andy5211d/Standig-899D/Pictures/IMG_0624.JPG

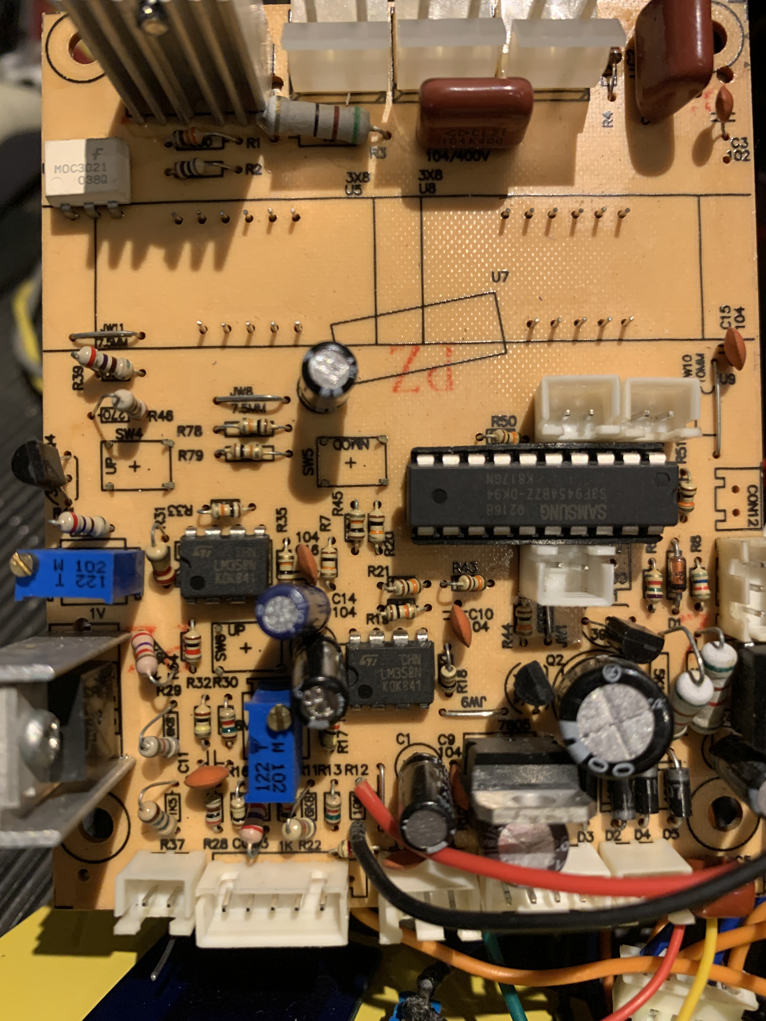
Pictures/IMG_0624.JPG
