andy5211d/Standig-899D/Pictures/IMG_0712.JPG

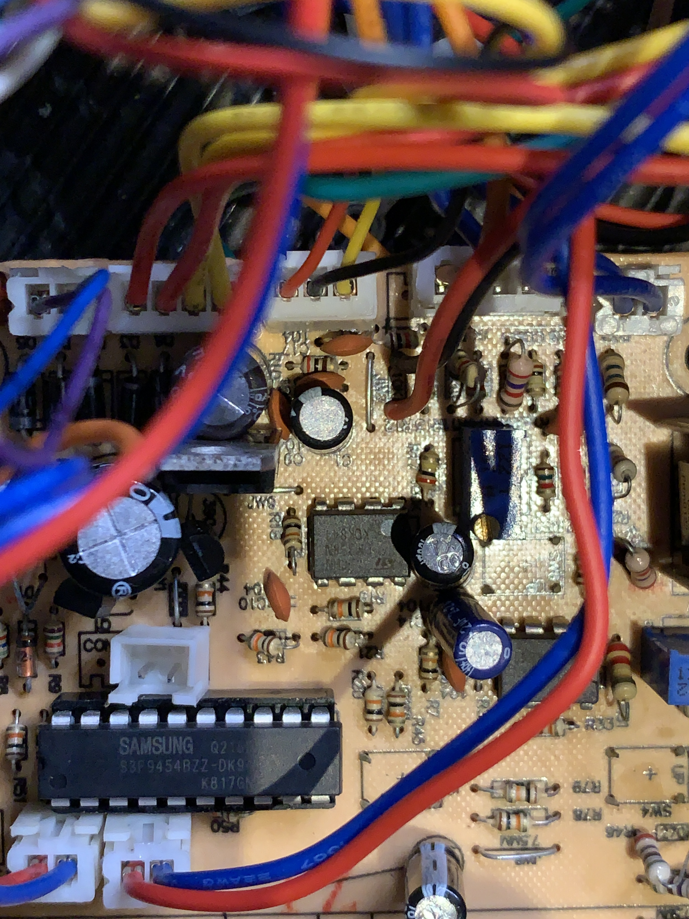
Pictures/IMG_0712.JPG
