andy5211d/Standig-899D/Pictures/IMG_0713.JPG

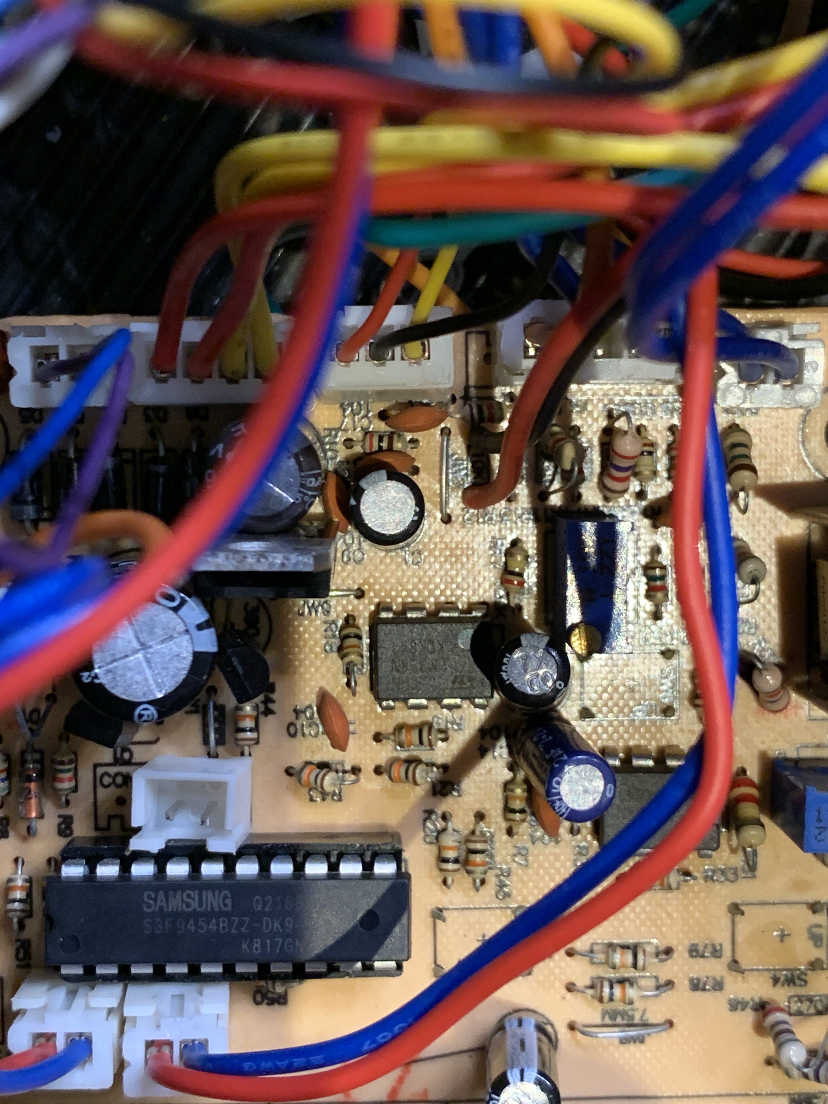
Pictures/IMG_0713.JPG
