andy5211d/Standig-899D/Pictures/IMG_0714.JPG

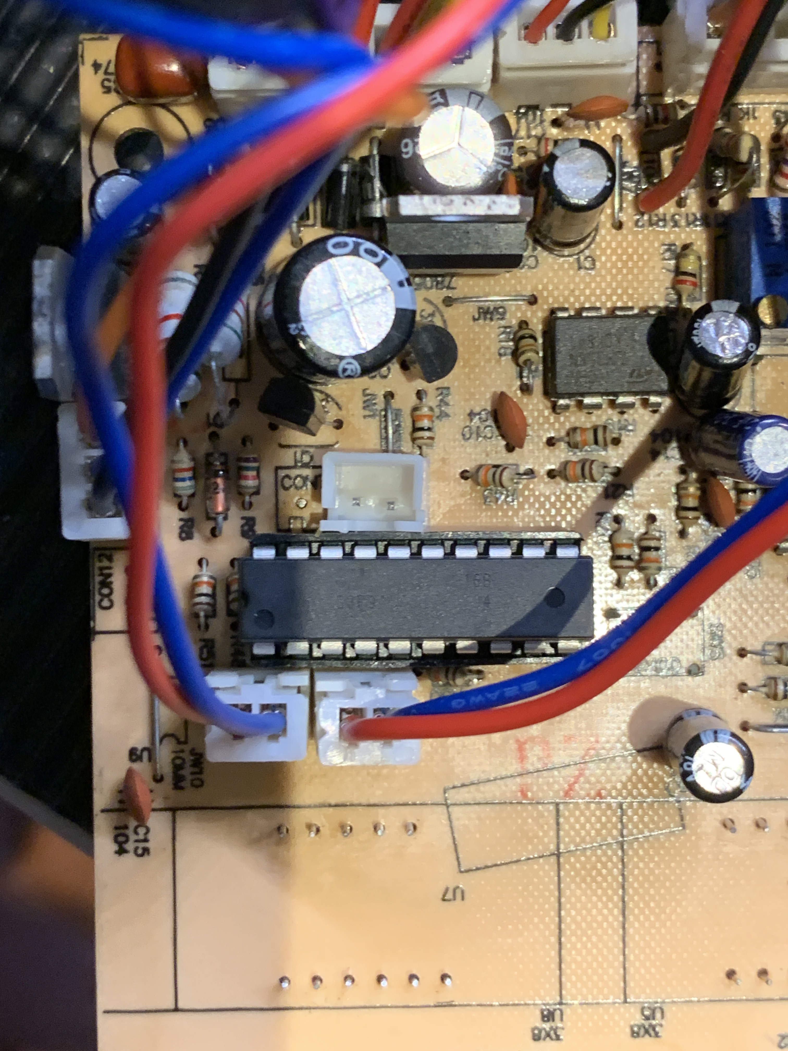
Pictures/IMG_0714.JPG
