andy5211d/Standig-899D/Pictures/IMG_0717.JPG

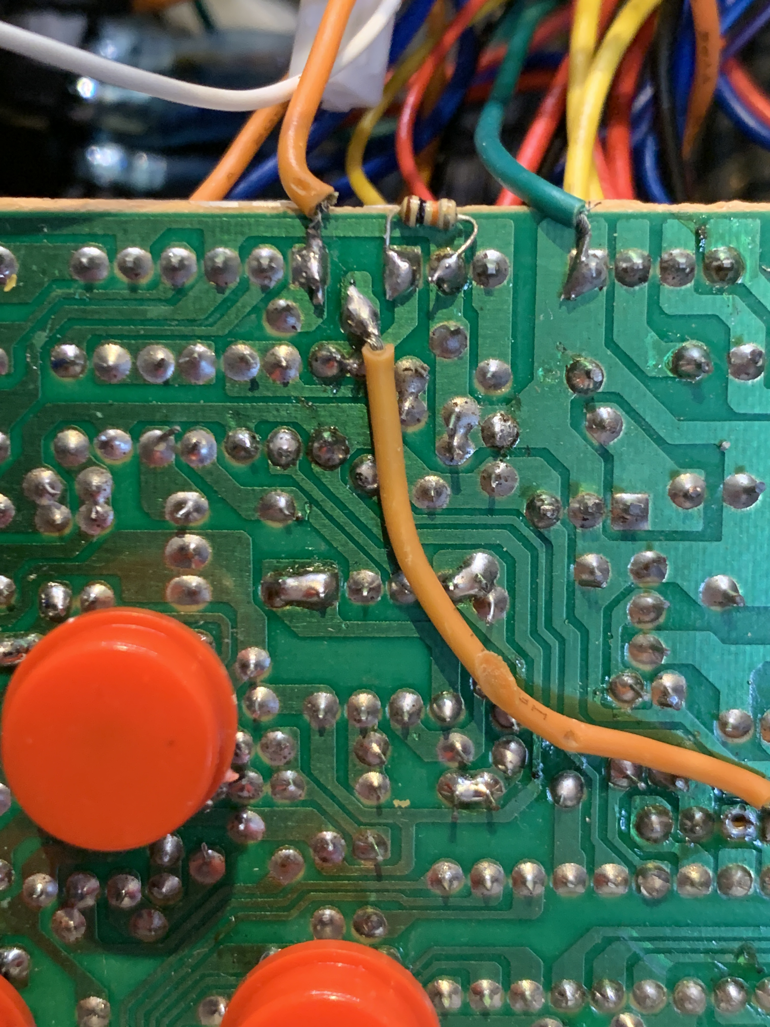
Pictures/IMG_0717.JPG
