andy5211d/Standig-899D/Pictures/IMG_0718.JPG

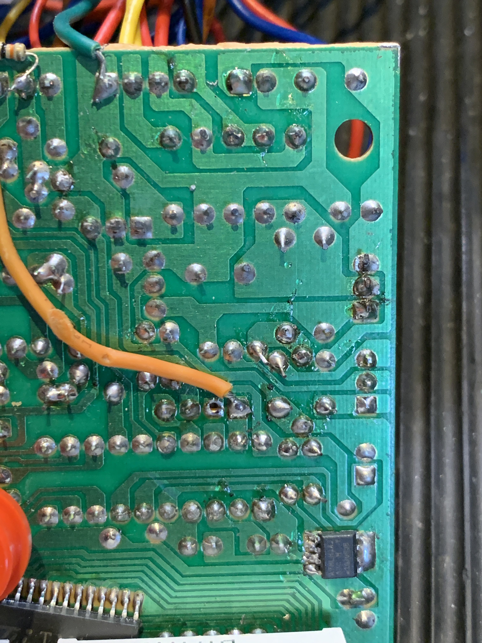
Pictures/IMG_0718.JPG
