andy5211d/Standig-899D/Pictures/IMG_0719.JPG

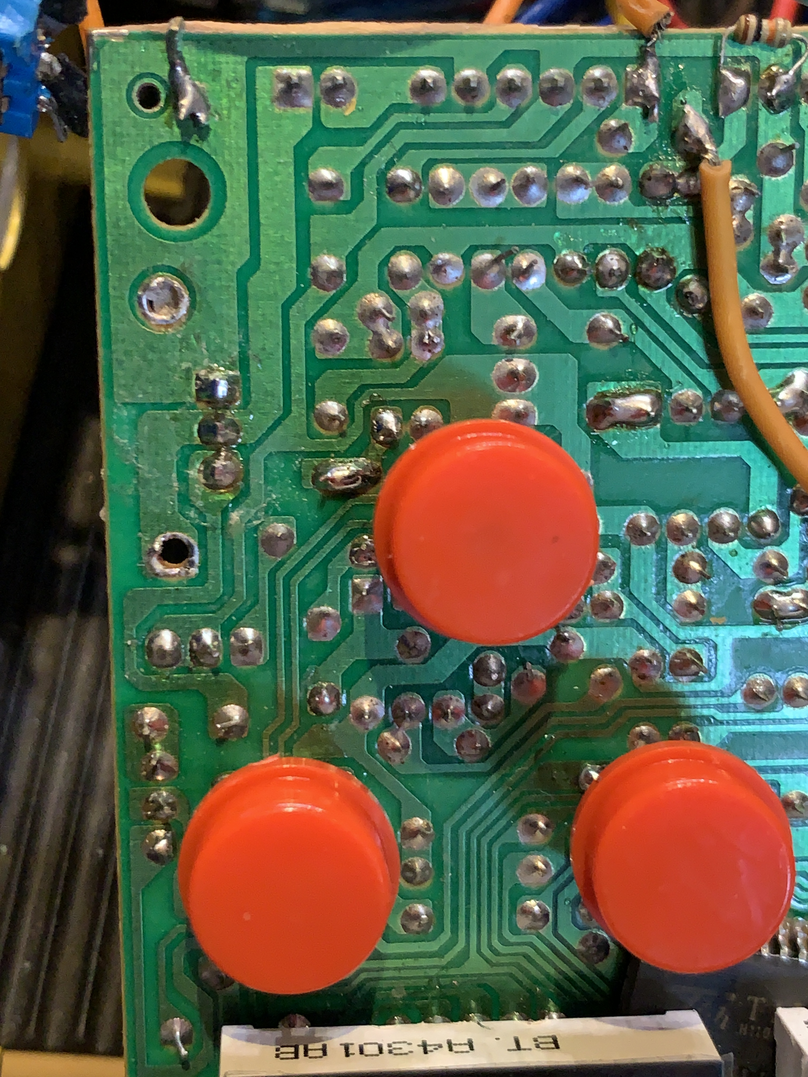
Pictures/IMG_0719.JPG
