andy5211d/Standig-899D/Pictures/IMG_0721.JPG

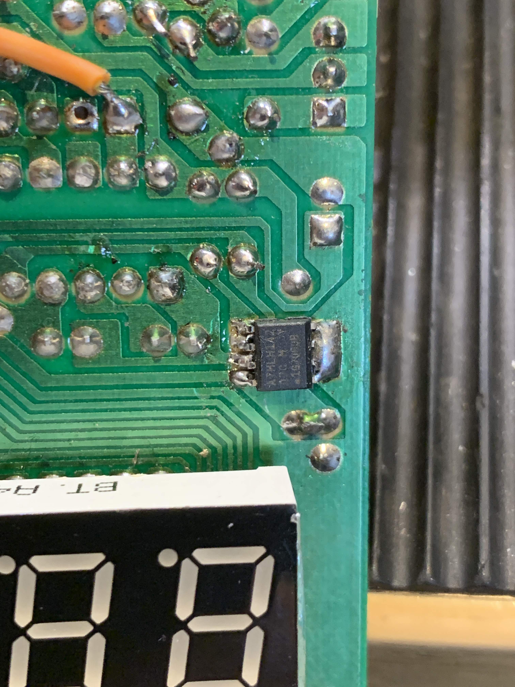
Pictures/IMG_0721.JPG
