andy5211d/Standig-899D/schematic/899d.kicad_sch

## KiCad design schematic/899d.kicad_sch (2024-03-28)

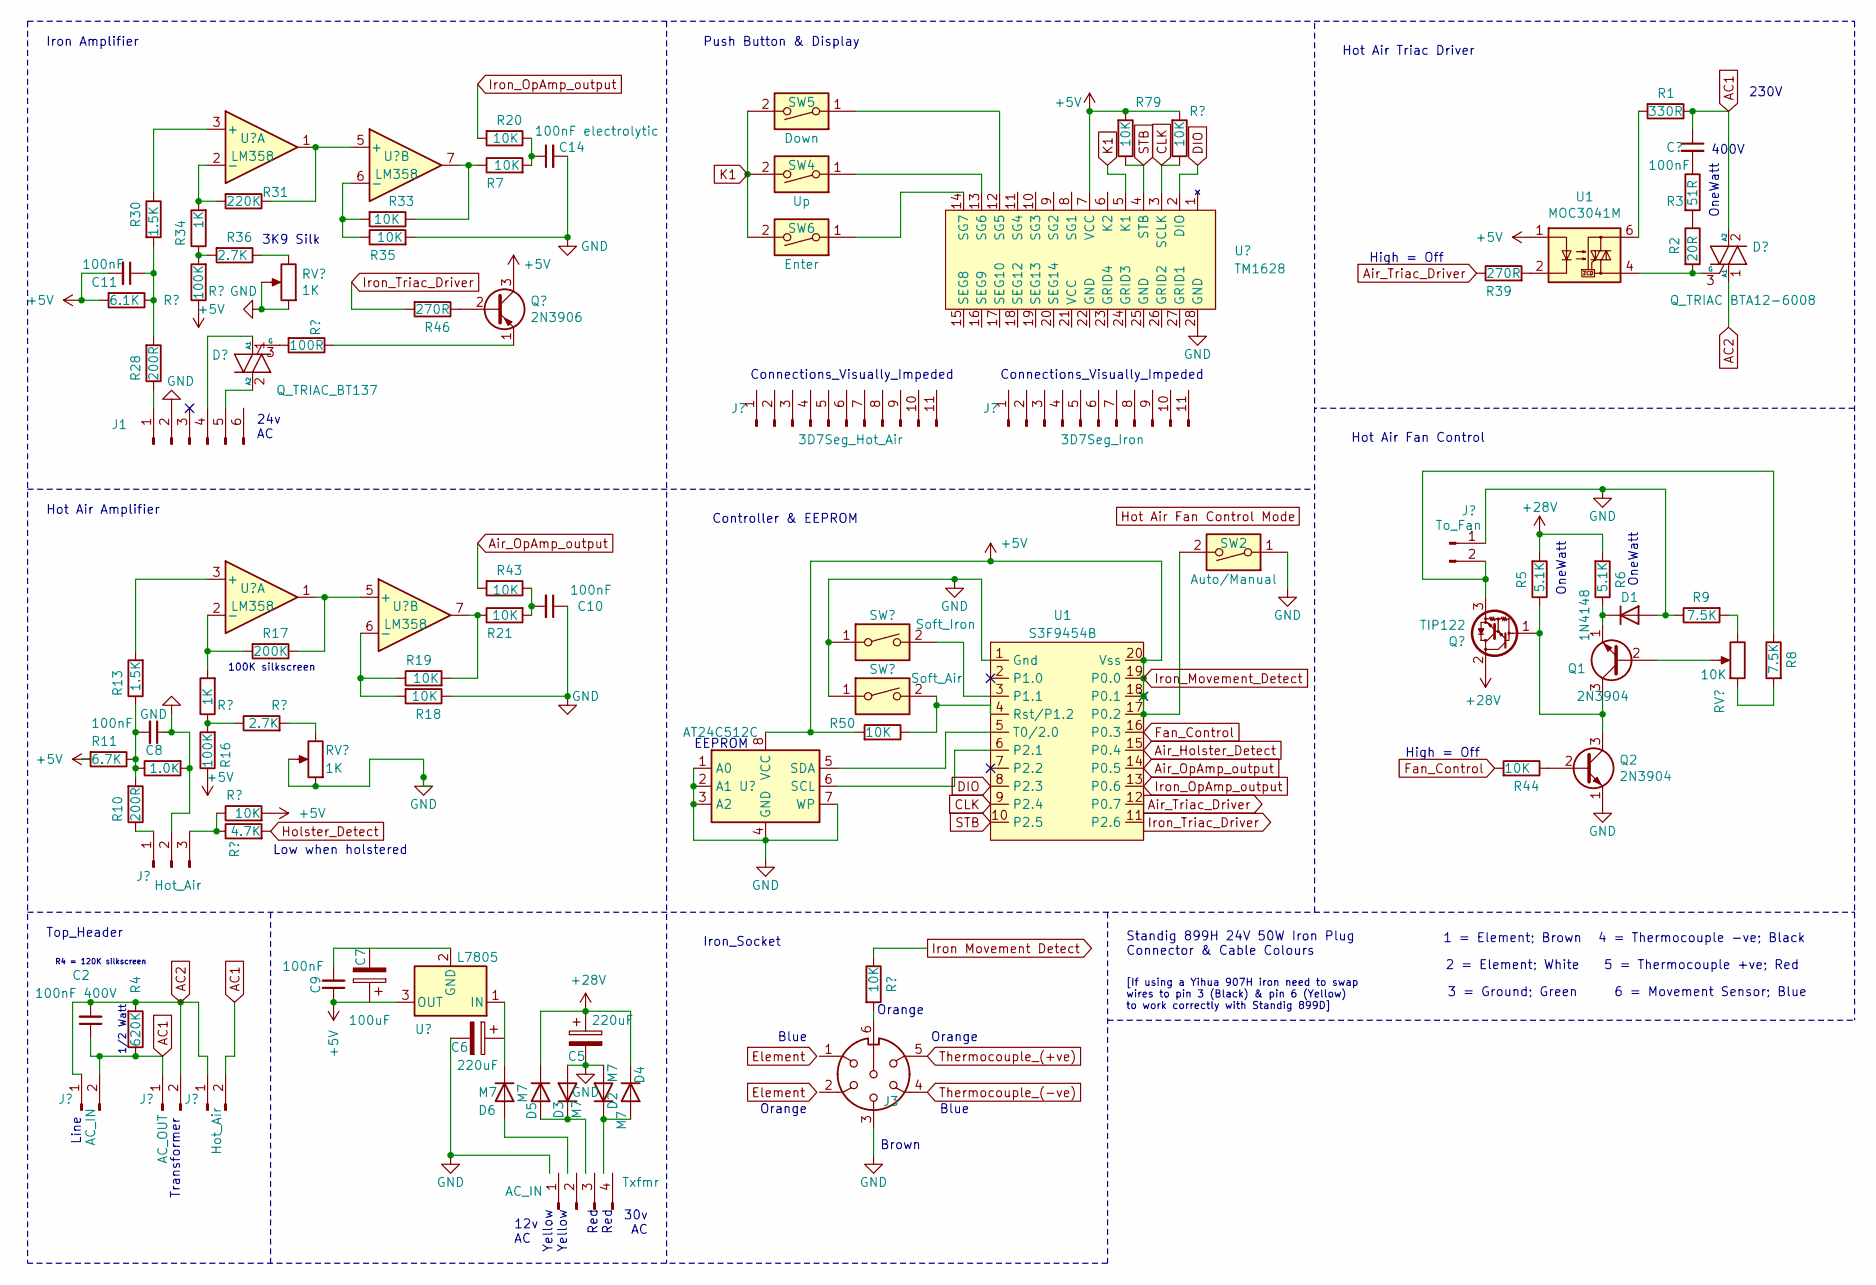
[picture p19: schematic 899d.kicad_sch]

Parts:
C2: 100nF 400V
C5, C6: 220uF
C7: 100uF
C8, C9, C10, C11: 100nF
C14: 100nF electrolytic
D1: 1N4148; D_DO-35_SOD27_P7.62mm_Horizontal
D2, D3, D4, D5, D6: M7; D_DO-41_SOD81_P10.16mm_Horizontal
J1, J3: (no value)
Q1, Q2: 2N3904; TO-92_Inline
R1: 330R
R2: 20R
R3: 51R
R4: 620K
R5, R6: 5.1K
R7, R18, R19, R20, R21, R33, R35, R43, R44, R50, R79: 10K
R8, R9: 7.5K
R10, R28: 200R
R11: 6.7K
R13, R30: 1.5K
R16: 100K
R17: 200K
R31: 220K
R34: 1K
R36: 2.7K
R39, R46: 270R
SW2: Auto/Manual
SW4: Up
SW5: Down
SW6: Enter
Txfmr: AC_IN
U1: MOC3041M

Connections:
AC1: C2.1, R1.1, R4.1
AC2: C2.2, R4.2
Air_Holster_Detect: U1.15 (P0.4)
Air_OpAmp_output: R43.2, U1.14 (P0.5)
Air_Triac_Driver: R39.1, U1.12 (P0.7)
CLK: U1.9 (P2.4)
DIO: U1.8 (P2.3)
Fan_Control: R44.2, U1.16 (P0.3)
GND: J3.3, SW2.1
Iron_Movement_Detect: R50.2, SW2.2, U1.17 (P0.2), U1.18 (P0.1), U1.19 (P0.0), U1.20 (Vss)
Iron_OpAmp_output: R20.2, U1.13 (P0.6)
Iron_Triac_Driver: R46.2, U1.11 (P2.6)
K1: SW4.2, SW5.2, SW6.2
unnamed: C5.1, D4.1 (K), D5.1 (K)
unnamed: C5.2, D2.2 (A), D3.2 (A)
unnamed: C8.1, R3.2
unnamed: C8.2, R3.1, R10.2, R11.1, R13.1
unnamed: C10.1, R18.1
unnamed: C10.2, R21.2, R43.1
unnamed: C11.1, R28.2, R30.2
unnamed: C14.1, R7.2, R20.1
unnamed: C14.2, R35.2
unnamed: D1.1 (K), Q1.1 (E), R6.1
unnamed: D1.2 (A), R9.1
unnamed: D2.1 (K), D4.2 (A)
unnamed: D3.1 (K), D5.2 (A)
unnamed: J1.1, R28.1
unnamed: Q1.3 (C), Q2.3 (C), R5.1
unnamed: Q2.2 (B), R44.1
unnamed: R1.2, U1.6 (P2.1)
unnamed: R2.1, R3.2
unnamed: R2.2, U1.4 (Rst/P1.2)
unnamed: R5.2, R6.2
unnamed: R18.2, R19.1
unnamed: R19.2, R21.1
unnamed: R31.2, R34.2
unnamed: R7.1, R33.1
unnamed: R33.2, R35.1
unnamed: R34.1, R36.2
unnamed: R39.2, U1.2 (P1.0)
unnamed: R50.1, U1.4 (Rst/P1.2)
STB: R79.1, U1.10 (P2.5)

Notes on the sheet:
12v AC
High = Off
Hot Air Triac Driver
Blue
400V
Yellow Yellow
4 = Thermocouple -ve; Black
Standig 899H 24V 50W Iron Plug Connector & Cable Colours
OneWatt
Hot Air Fan Control
EEPROM
3 = Ground; Green
100K silkscreen
1/2 Watt
1 = Element; Brown
[If using a Yihua 907H iron need to swap wires to pin 3 (Black) & pin 6 (Yellow) to work correctly with Standig 899D]
230V
Brown
5 = Thermocouple +ve; Red
Line
Low when holstered
Orange
24v AC
30v AC
Connections_Visually_Impeded
Push Button & Display
Transformer
3K9 Silk
Iron Amplifier
Iron_Socket
R4 = 120K silkscreen
2 = Element; White
6 = Movement Sensor; Blue
Hot Air Amplifier
Controller & EEPROM
Red Red
Top_Header
