andy5211d/Standig-899D/Pictures/IMG_0621.JPG

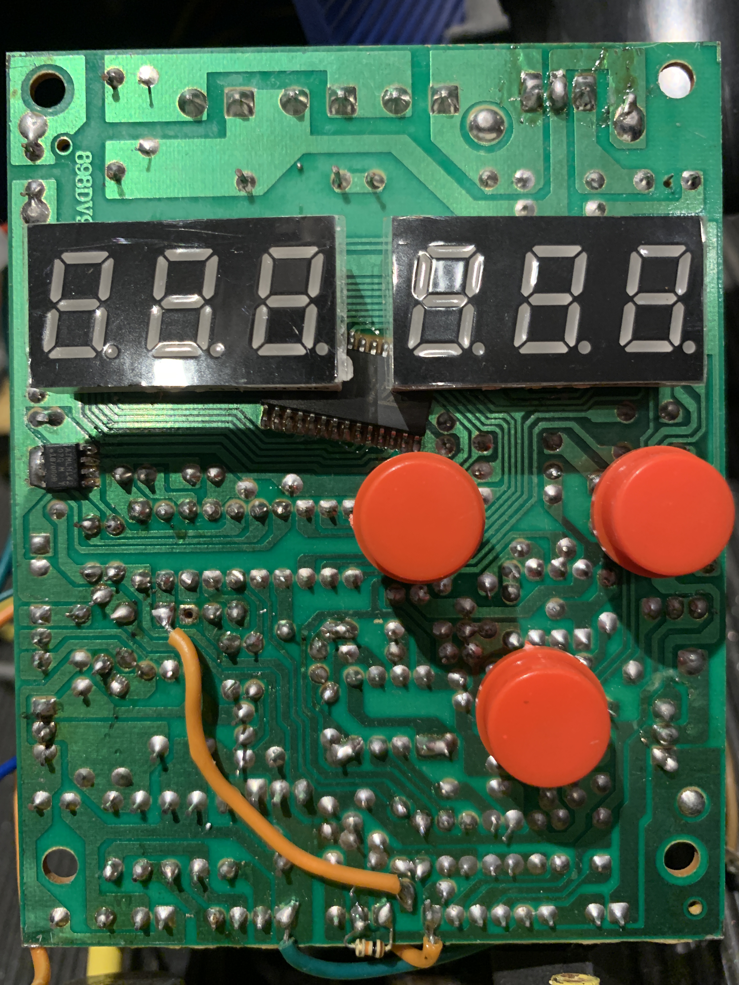
Pictures/IMG_0621.JPG
