andy5211d/Standig-899D/Pictures/IMG_0622.JPG

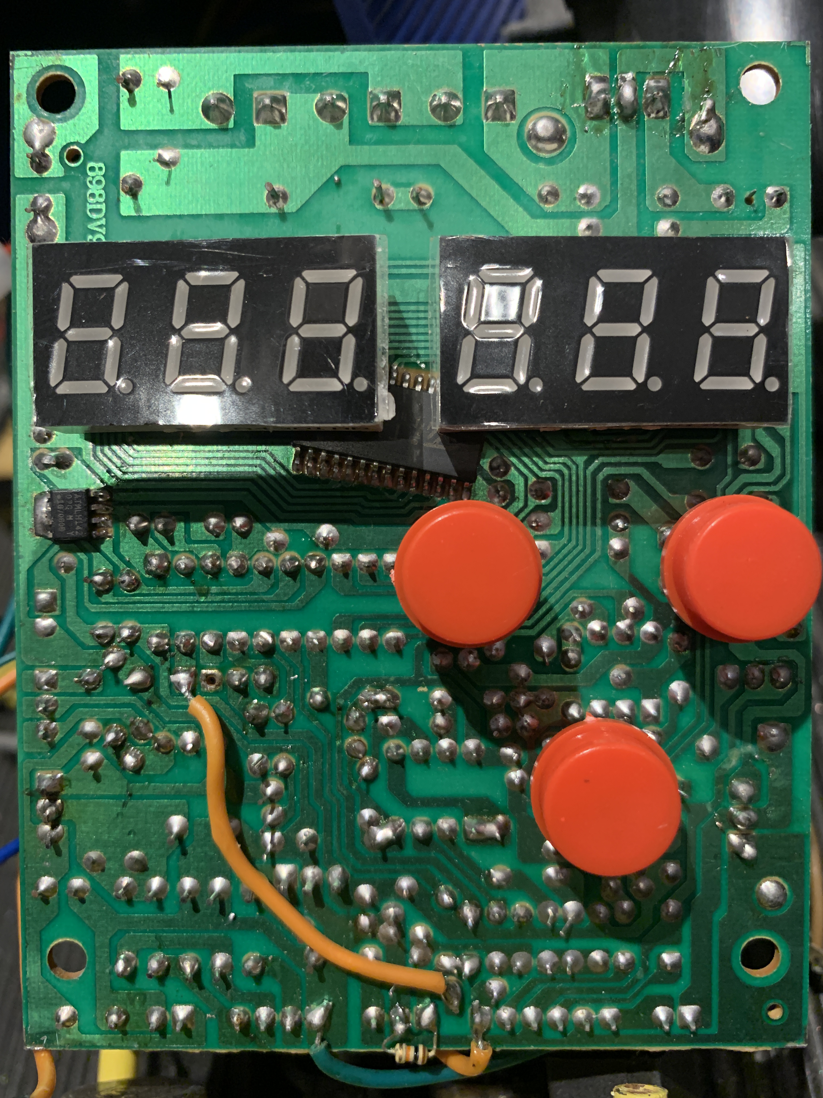
Pictures/IMG_0622.JPG
