andy5211d/Standig-899D/Pictures/IMG_0623.JPG

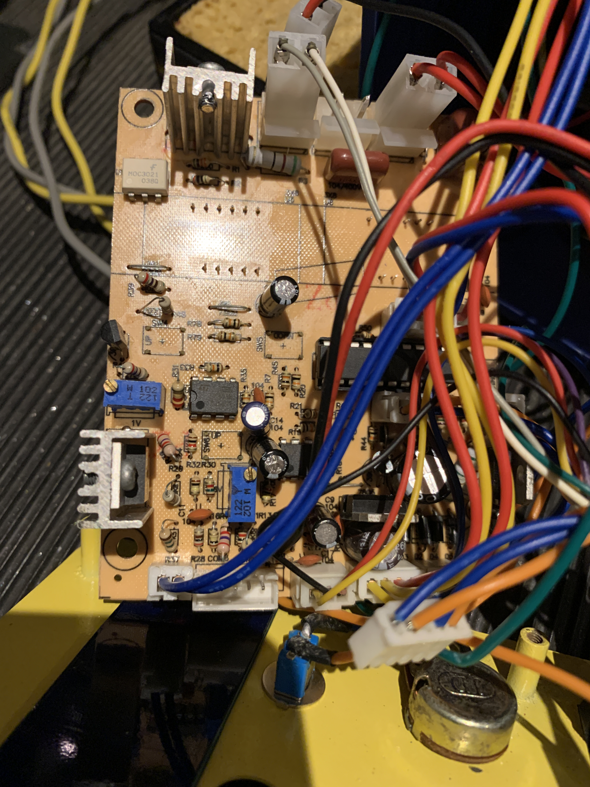
Pictures/IMG_0623.JPG
