andy5211d/Standig-899D/Pictures/IMG_0625.JPG

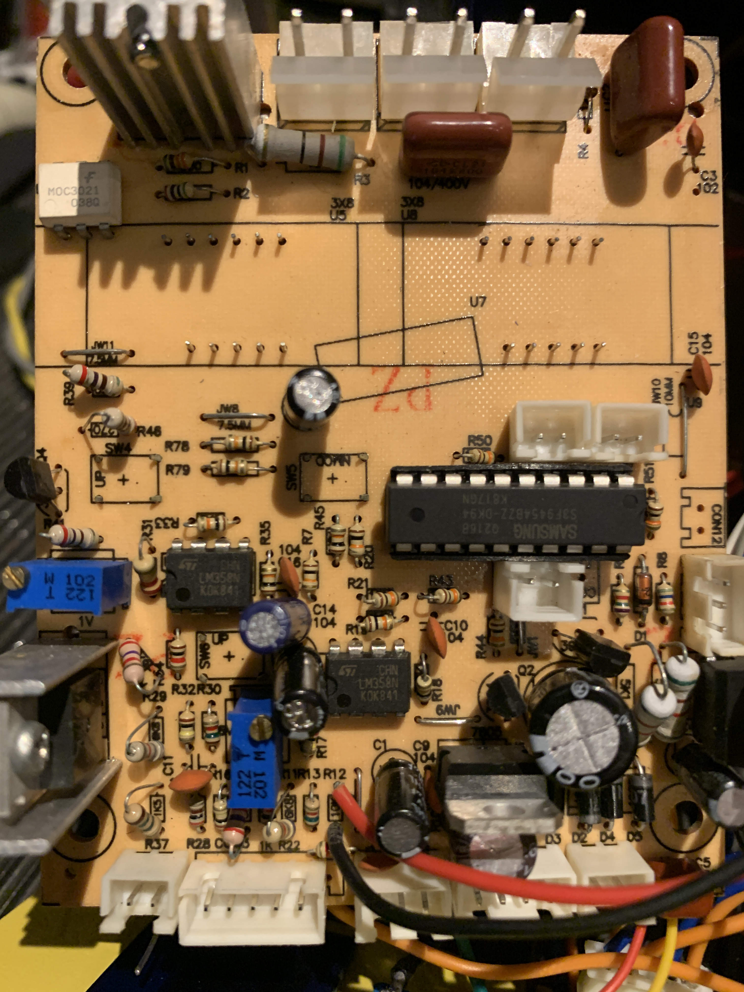
Pictures/IMG_0625.JPG
