andy5211d/Standig-899D/Pictures/IMG_0716.JPG

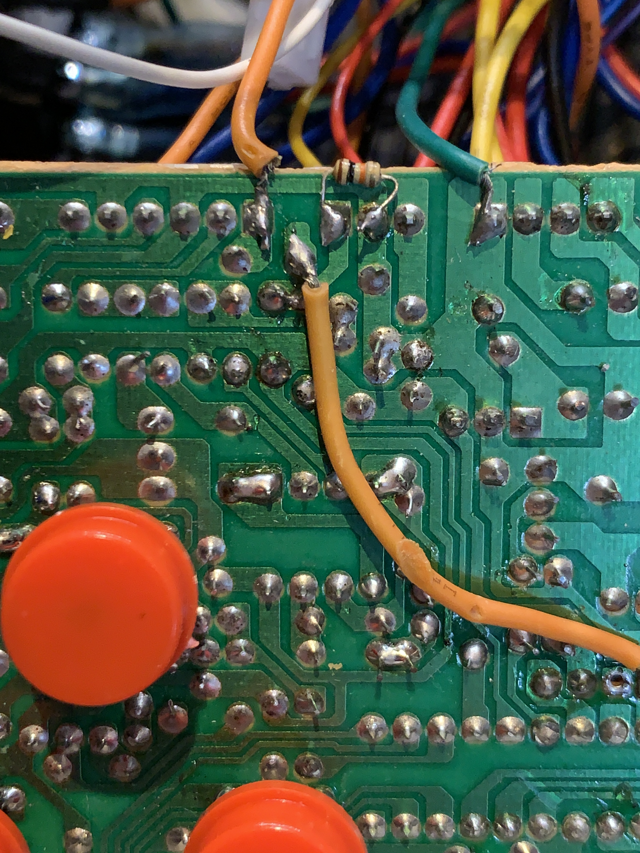
Pictures/IMG_0716.JPG
