andy5211d/Standig-899D/Pictures/IMG_0729.JPG

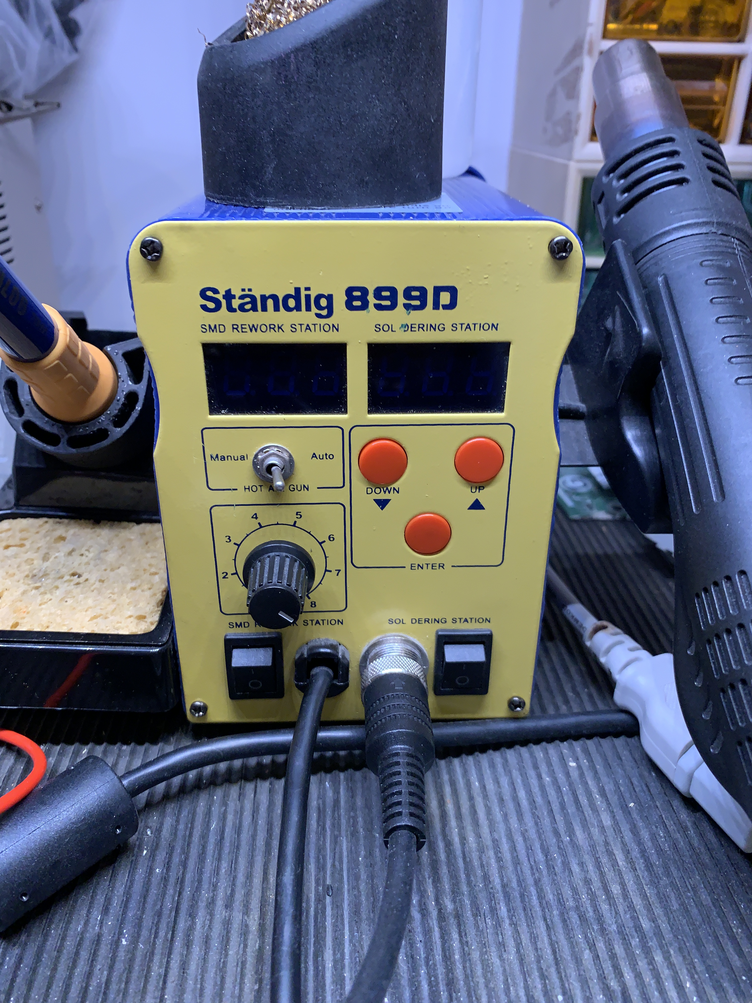
Pictures/IMG_0729.JPG
